mengstr/aytabtu/DiyLC/ROMdecoder1.png

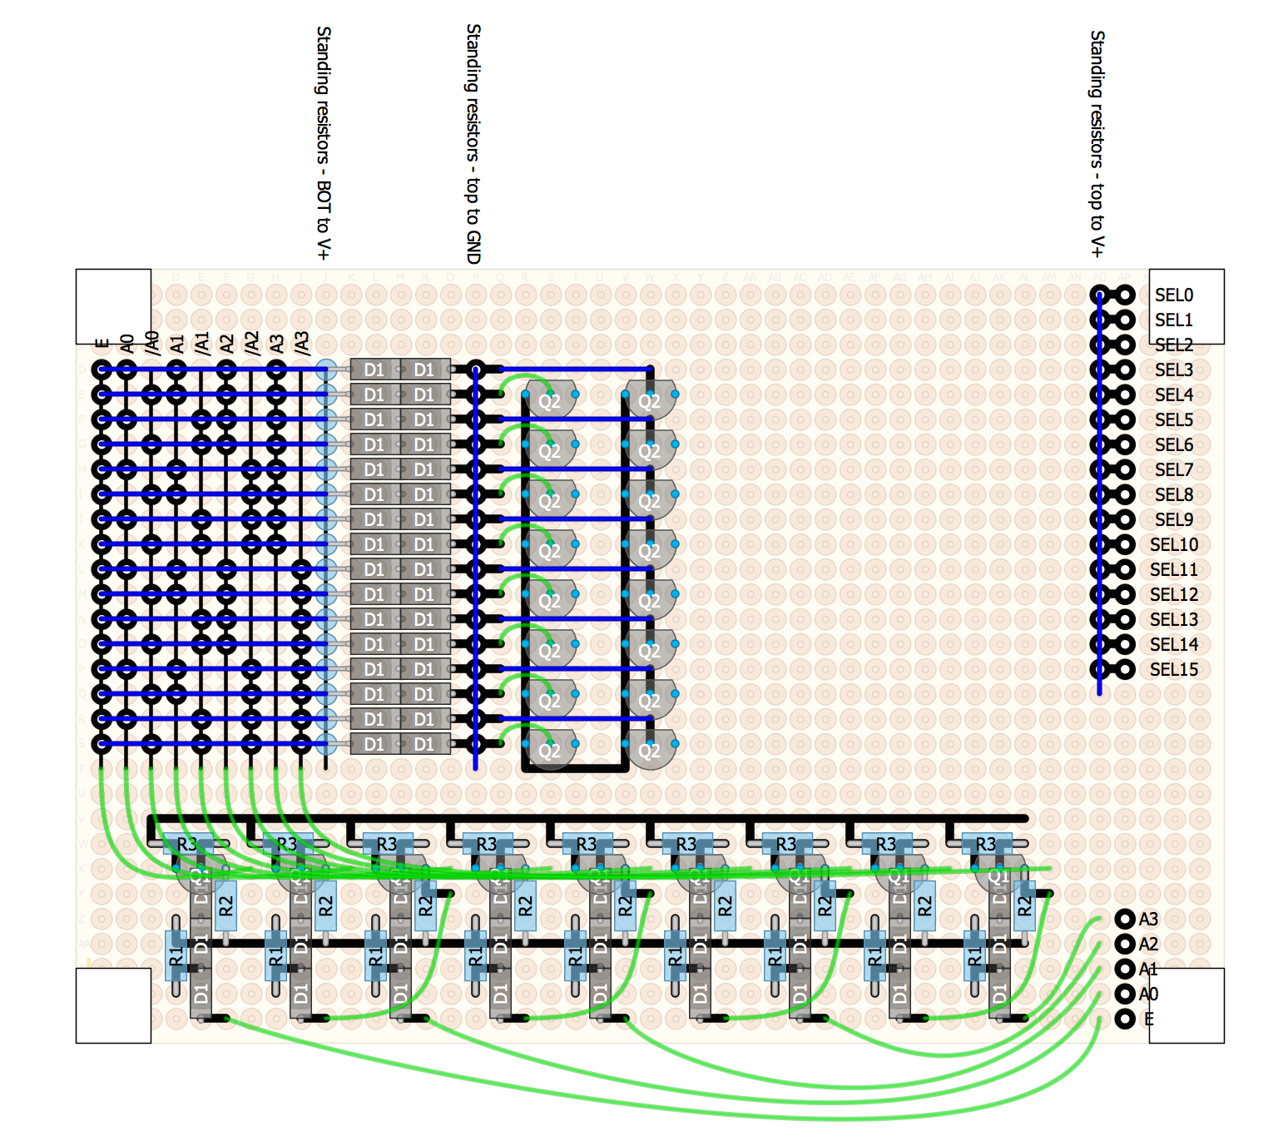
DiyLC/ROMdecoder1.png
