mengstr/aytabtu/DiyLC/UART-RX-D-LATCH.png

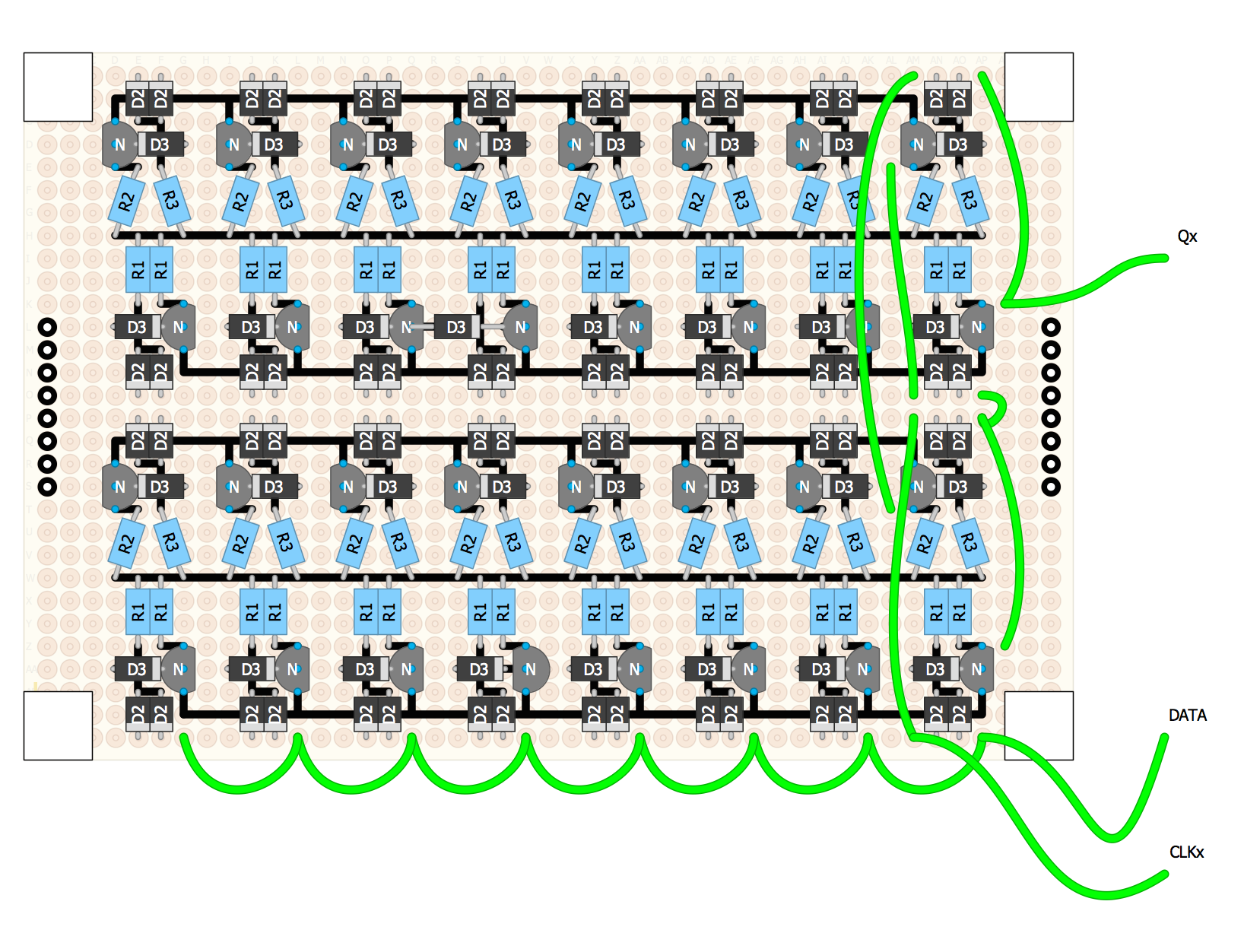
DiyLC/UART-RX-D-LATCH.png
