mengstr/aytabtu/DiyLC/UART-TX-RingCounter.png

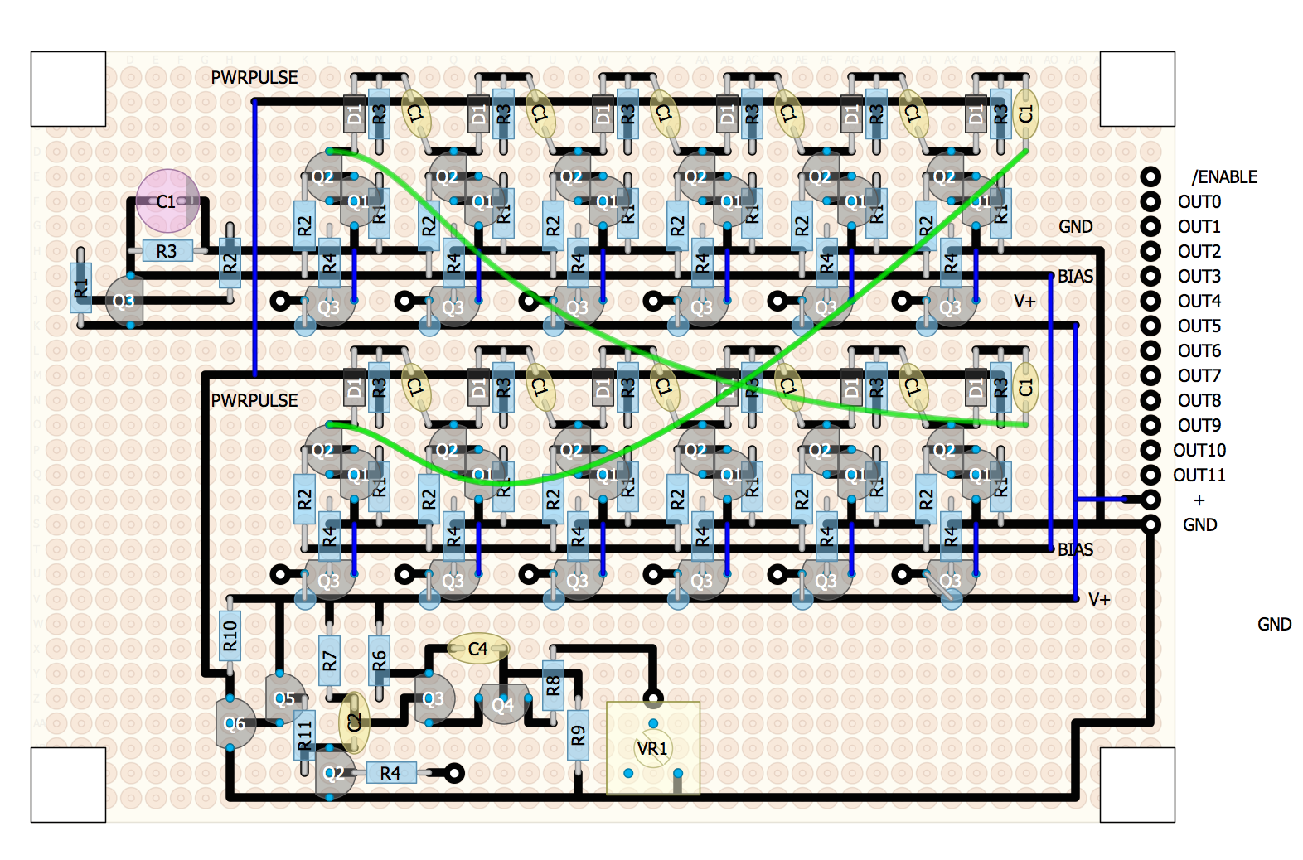
DiyLC/UART-TX-RingCounter.png
