mengstr/aytabtu/Images/4-to-16decoder-detail.jpg

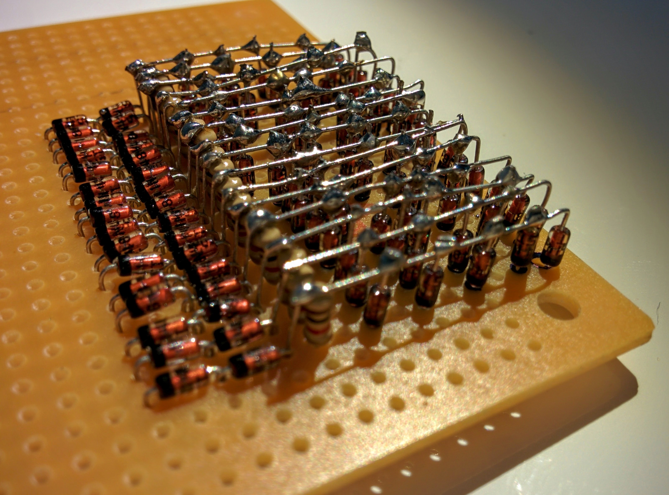
Images/4-to-16decoder-detail.jpg
