mengstr/aytabtu/Images/BusMonitorLeds.jpg

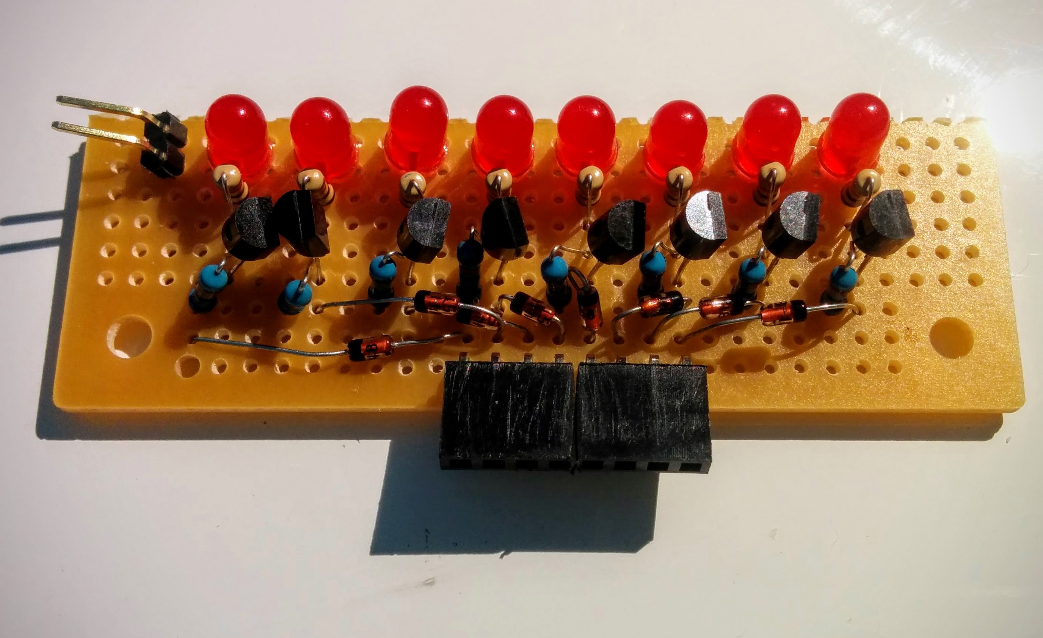
Images/BusMonitorLeds.jpg
