mengstr/aytabtu/Images/ClockGen4Phase1.png

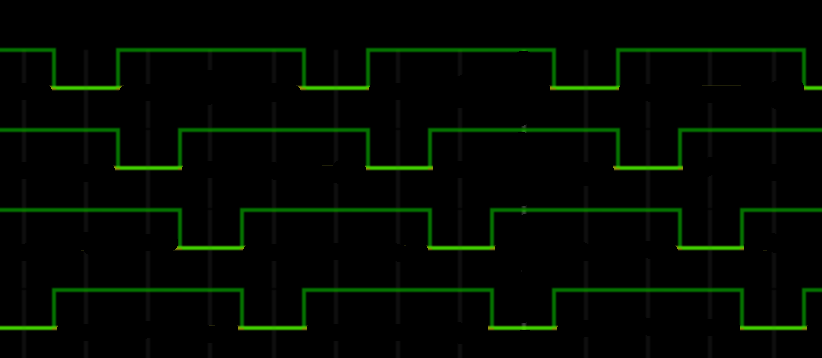
Images/ClockGen4Phase1.png
