mengstr/aytabtu/Images/ClockGenDiagram.png

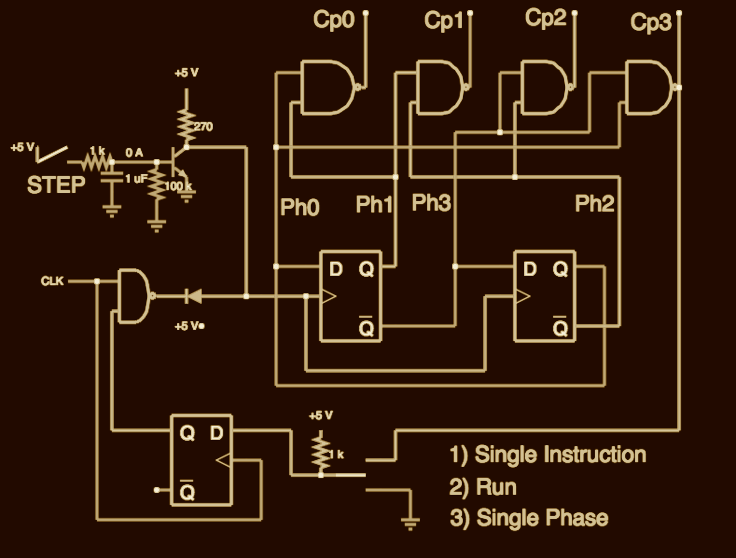
Images/ClockGenDiagram.png
