mengstr/aytabtu/Images/ClockGenPCB.jpg

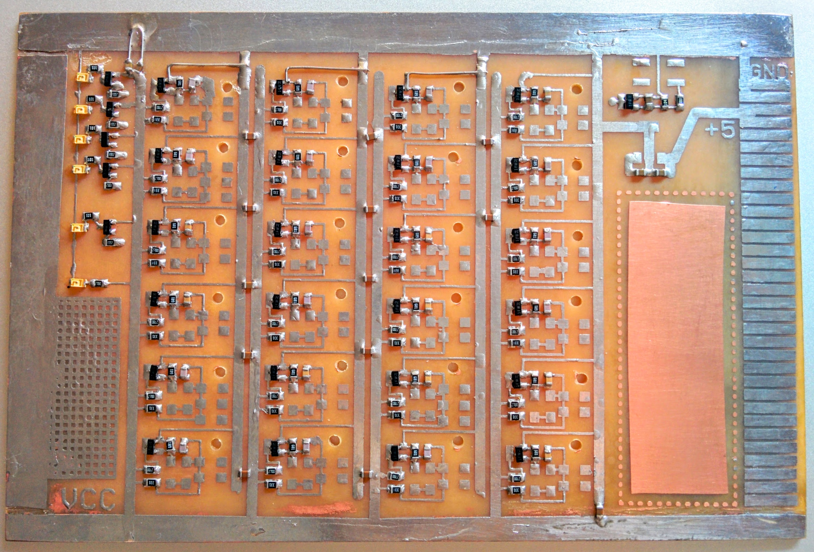
Images/ClockGenPCB.jpg
