mengstr/aytabtu/Images/ClockGenPCBdetail.jpg

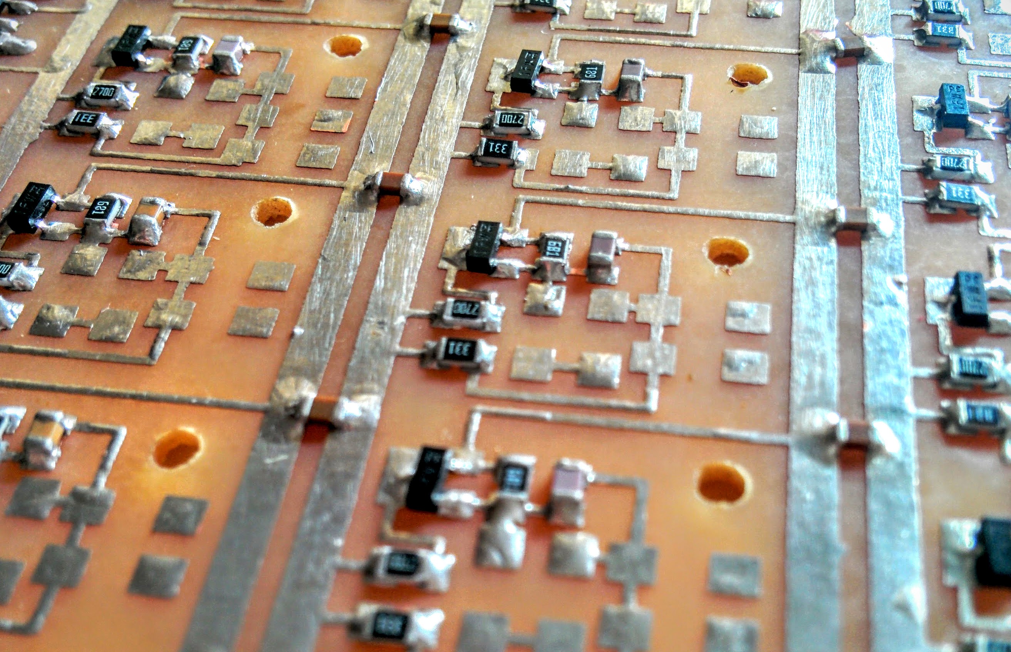
Images/ClockGenPCBdetail.jpg
