mengstr/aytabtu/Images/Divider-Scho.jpg

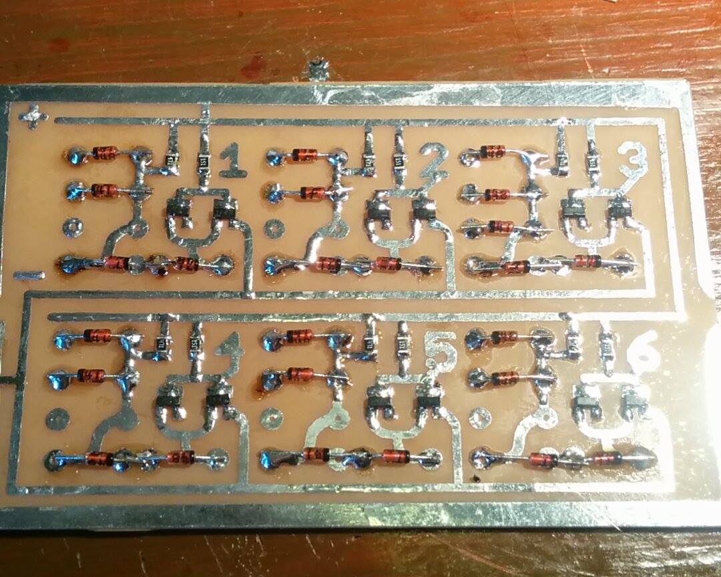
Images/Divider-Scho.jpg
