mengstr/aytabtu/Images/FastNandPCB.jpg

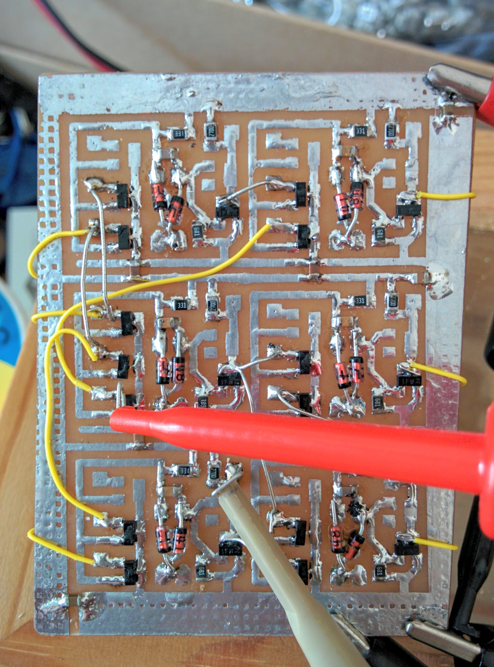
Images/FastNandPCB.jpg
