mengstr/aytabtu/Images/Hex4NANDs.jpg

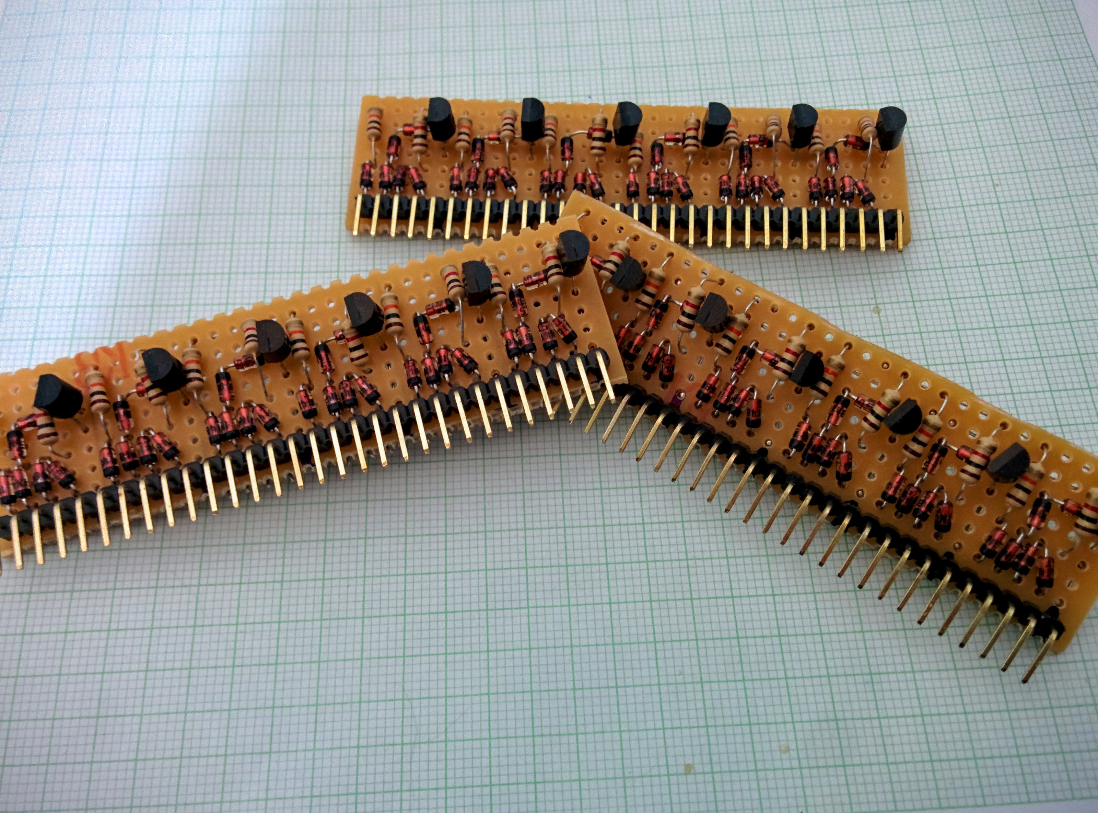
Images/Hex4NANDs.jpg
