mengstr/aytabtu/Images/NAND2_5v.png

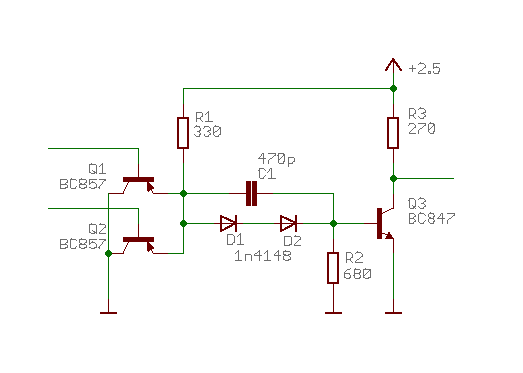
Images/NAND2_5v.png
