mengstr/aytabtu/Images/OctalTransparentDlatch-Bot.jpg

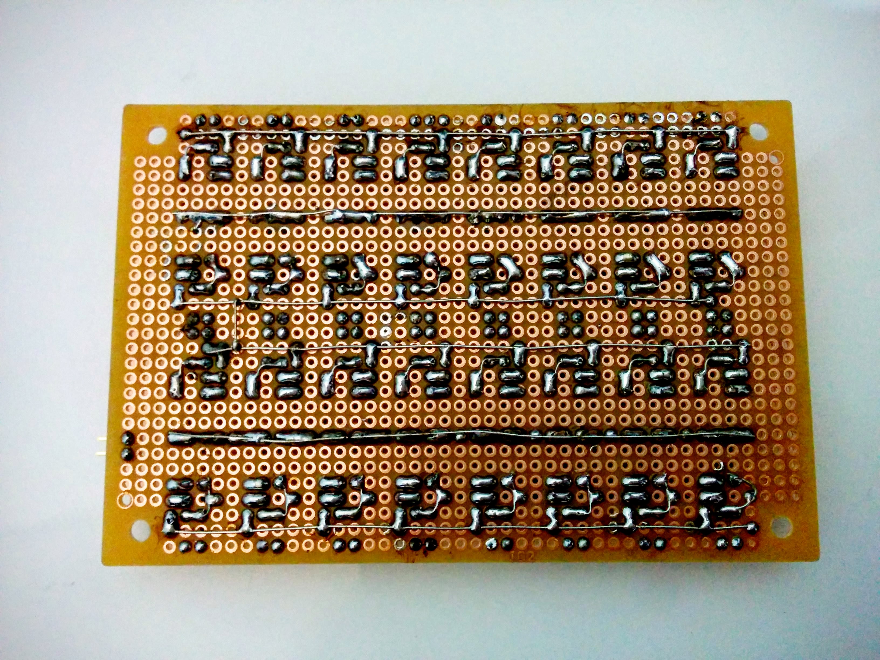
Images/OctalTransparentDlatch-Bot.jpg
