mengstr/aytabtu/Images/OctalTransparentDlatch-Top.jpg

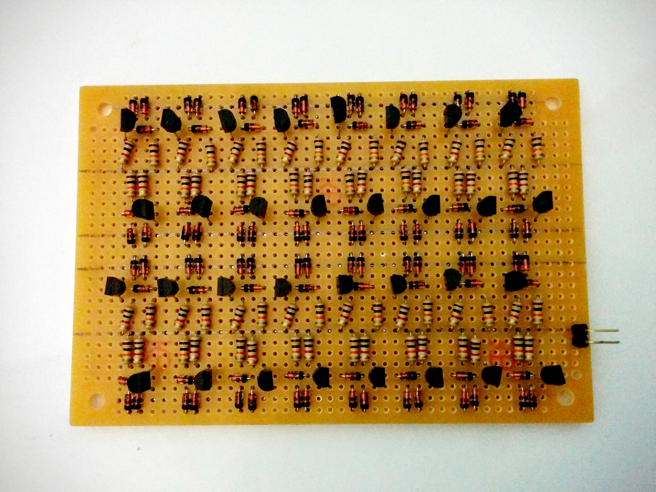
Images/OctalTransparentDlatch-Top.jpg
