mengstr/aytabtu/Images/UART-RX internal module routing.png

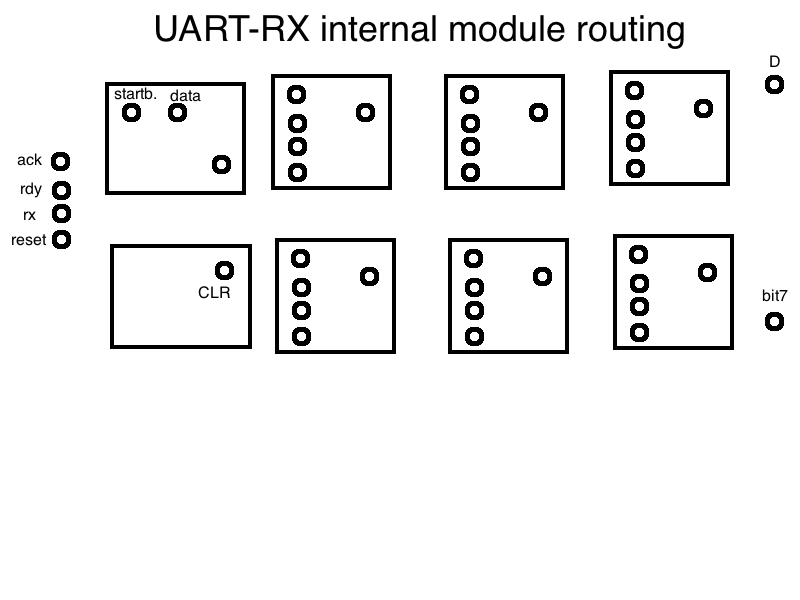
Images/UART-RX internal module routing.png
