mengstr/aytabtu/Images/UART-RX-D-LATCH.png

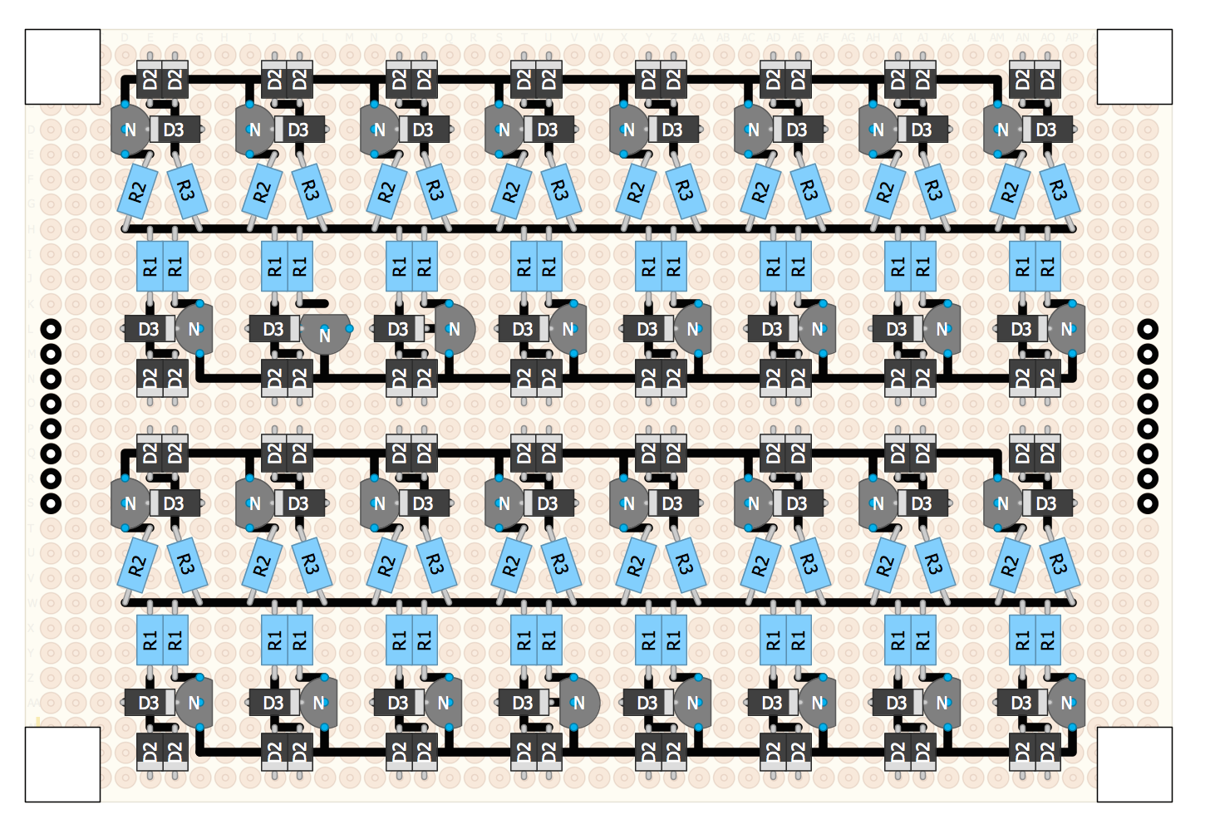
Images/UART-RX-D-LATCH.png
