mengstr/aytabtu/Images/UART-RX-timing1.jpg

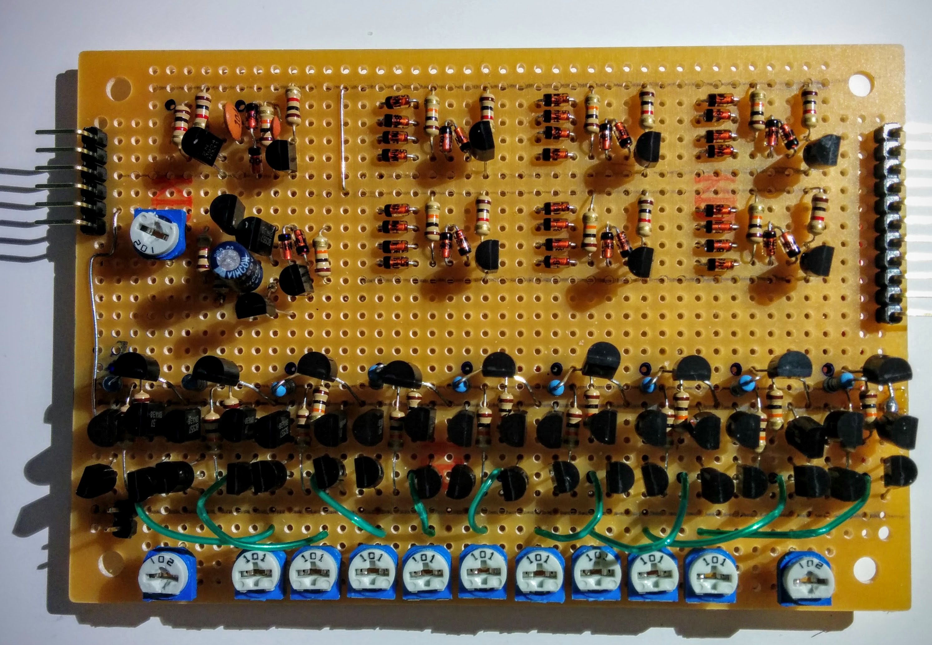
Images/UART-RX-timing1.jpg
