mengstr/aytabtu/Images/UART-RX-timing2.jpg

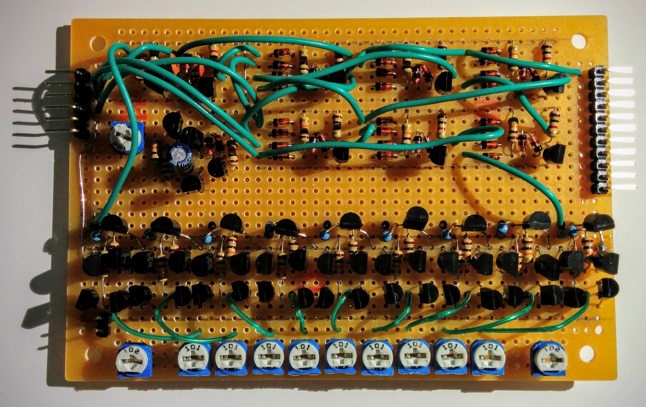
Images/UART-RX-timing2.jpg
