mengstr/aytabtu/Images/UART-TX-RingCounter.png

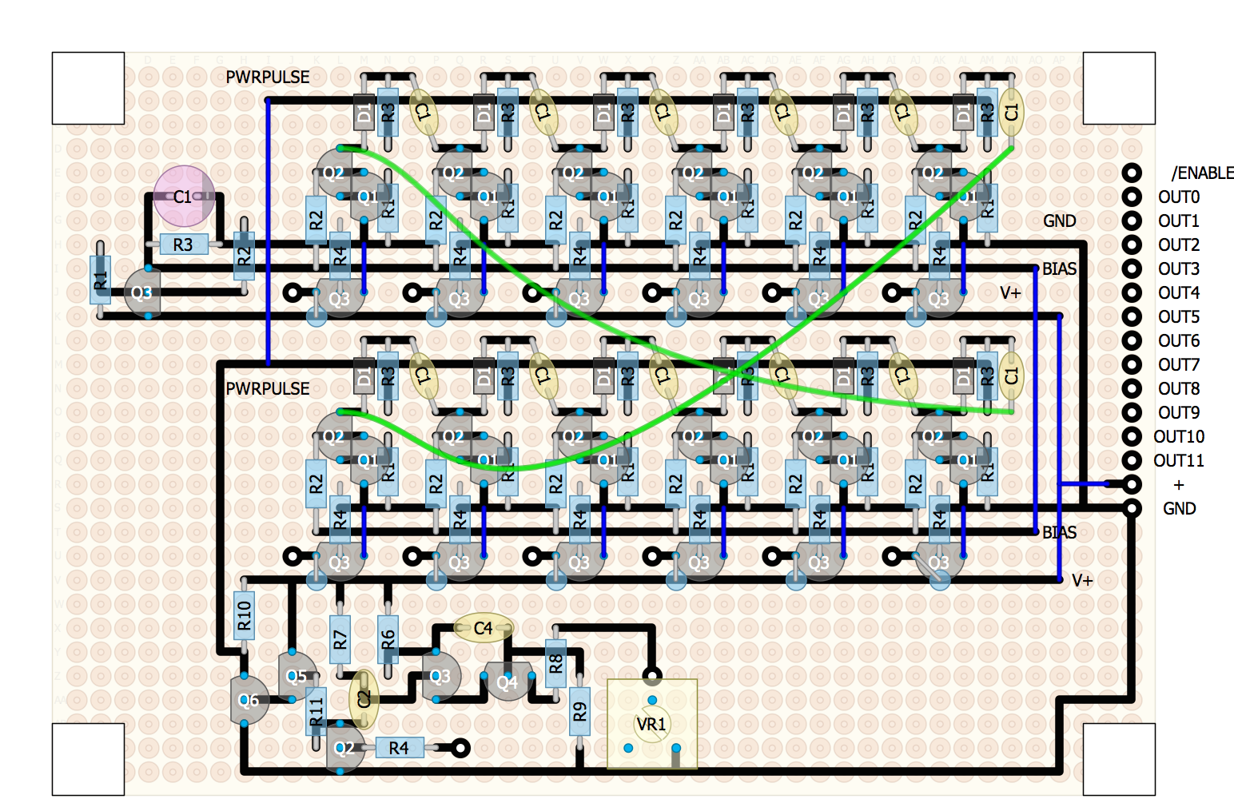
Images/UART-TX-RingCounter.png
