mengstr/aytabtu/Doc/InstructionSet.png

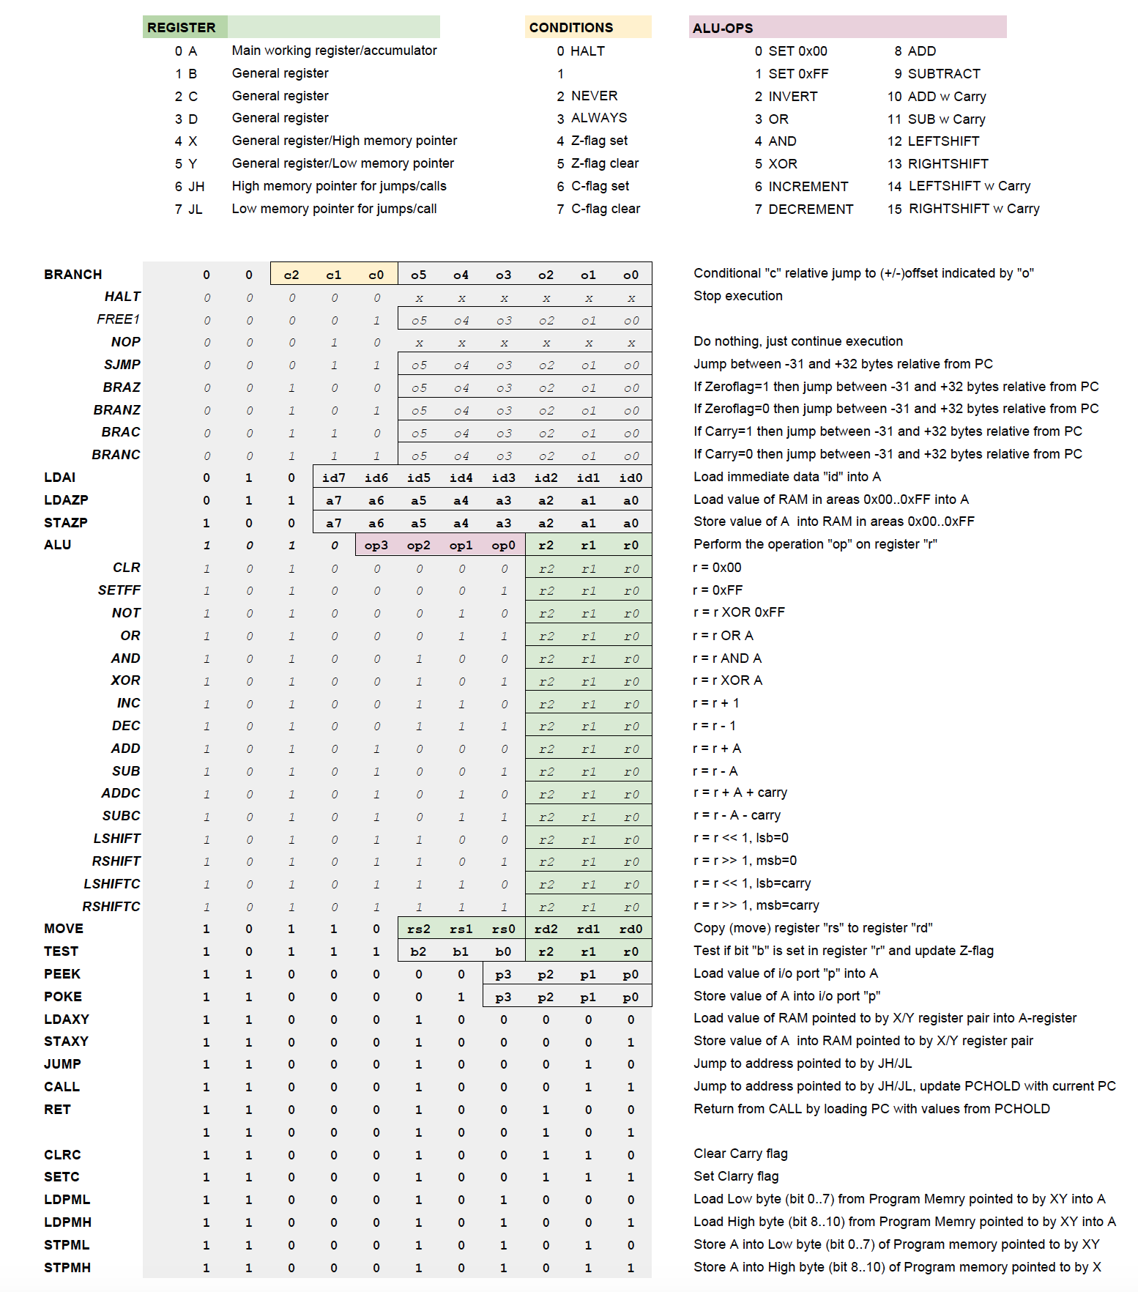
Doc/InstructionSet.png
