mengstr/aytabtu/Images/ALUSliceTest.jpg

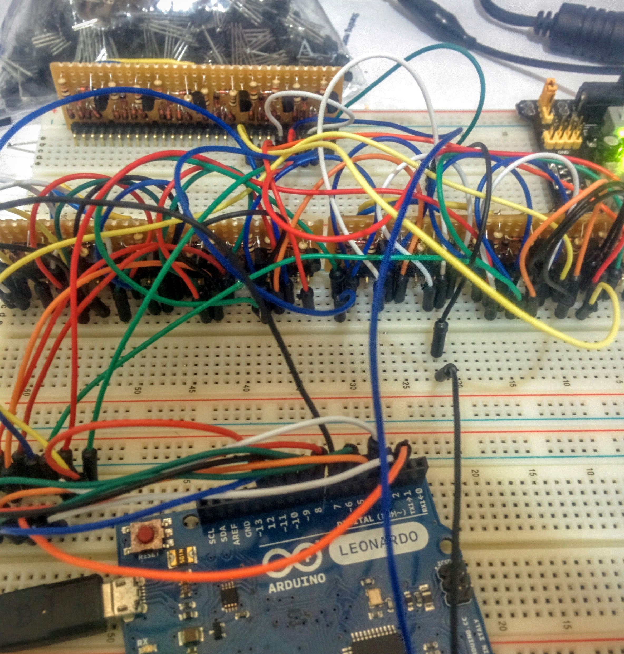
Images/ALUSliceTest.jpg
