mengstr/aytabtu/Images/TestingComparatorForUARTrx.jpg

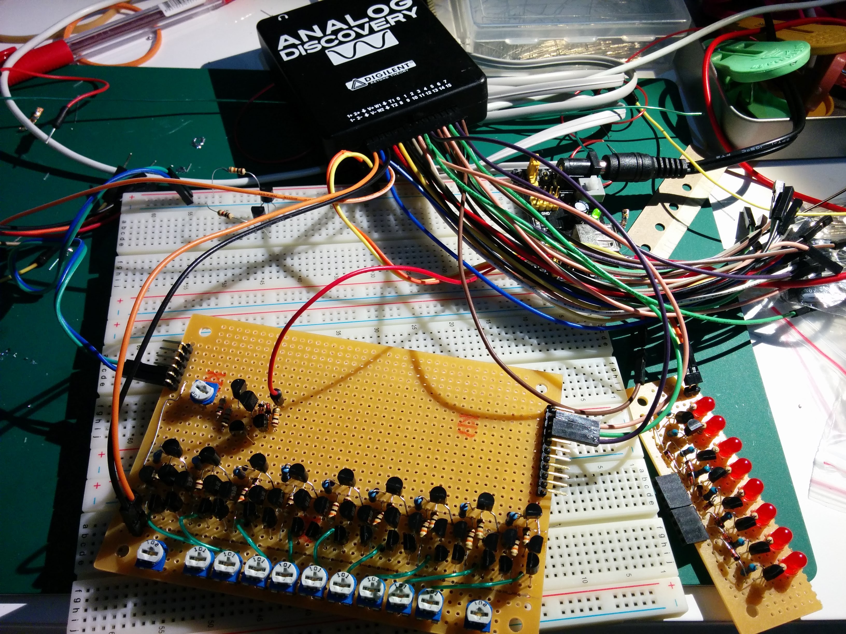
Images/TestingComparatorForUARTrx.jpg
