mengstr/aytabtu/Spice/Strip/Pmem-driver-test.asc

C1: cap; 1n
C2: cap; 100p
C3: cap; 100p
C4: cap; 100p
C5: cap; 100p
C6: cap; 100p
C7: cap; 100p
C8: cap; 100p
C9: cap; 100p
C10: cap; 100p
C11: cap; 100p
C12: cap; 100p
C13: cap; 100p
C14: cap; 100p
C15: cap; 100p
C16: cap; 100p
C17: cap; 100p
C18: cap; 100p
D1: schottky; BAT54
D2: diode; 1N4148
D3: schottky; BAT54
D4: diode; 1N4148
D5: schottky; BAT54
D6: diode; 1N4148
D7: schottky; BAT54
D8: schottky; BAT54
D9: diode; 1N4148
D10: diode; 1N4148
D11: schottky; BAT54
D12: diode; 1N4148
D13: schottky; BAT54
D14: diode; 1N4148
D15: schottky; BAT54
D16: diode; 1N4148
D17: schottky; BAT54
D18: diode; 1N4148
D19: schottky; BAT54
D20: diode; 1N4148
D21: schottky; BAT54
D22: diode; 1N4148
D23: schottky; BAT54
D24: diode; 1N4148
D25: schottky; BAT54
D26: diode; 1N4148
D27: schottky; BAT54
D28: diode; 1N4148
D29: schottky; BAT54
D30: diode; 1N4148
D31: schottky; BAT54
D32: diode; 1N4148
Q1: npn; BC847B
Q2: npn; BC847B
Q3: pnp; BC857B
Q4: npn; BC847B
Q5: npn; BC847B
Q6: npn; BC847B
Q7: npn; BC847B
Q8: npn; BC847B
Q9: npn; BC847B
Q10: npn; BC847B
Q11: npn; BC847B
Q12: npn; BC847B
Q13: npn; BC847B
Q14: npn; BC847B
Q15: npn; BC847B
Q16: npn; BC847B
Q17: npn; BC847B
Q18: npn; BC847B
R1: res; 150
R2: res; 470
R3: res; 470
R4: res; 150
R5: res; 470
R6: res; 150
R7: res; 150
R8: res; 470
R9: res; 470
R10: res; 150
R11: res; 470
R12: res; 150
R13: res; 470
R14: res; 150
R15: res; 470
R16: res; 150
R17: res; 470
R18: res; 150
R19: res; 470
R20: res; 150
R21: res; 470
R22: res; 150
R23: res; 470
R24: res; 150
R25: res; 470
R26: res; 150
R27: res; 470
R28: res; 150
R29: res; 470
R30: res; 150
R31: res; 470
R32: res; 150
R33: res; 470
V1: voltage; 3.3
V3: voltage; PULSE(3.3 0 0 1n 1n 300n 1u)
Named nets: 0, V+, WR, v+, in
.tran 3u
