mengstr/aytabtu/Spice/Strip/_FA1.asc

V1: voltage; PULSE(3.3 0 0 1n 1n 100n 200n)
V2: voltage; PULSE(3.2 0.1 0 1n 1n 200n 400n)
V3: voltage; PULSE(3.1 0.2 0 1n 1n 400n 800n)
V4: voltage; PULSE(3.1 0.2 0 1n 1n 2000n 4000n)
X1: FA1
Named nets: CO, SUM, 0, A, B, CI, /SUM
.tran 5888n
