mengstr/aytabtu/Spice/Tests/_PMemBoard.asc

D1: schottky; BAT54
D2: diode; 1N4148
D3: diode; 1N4148
D4: diode; 1N4148
D5: schottky; BAT54
D6: diode; 1N4148
D7: diode; 1N4148
D8: diode; 1N4148
D9: schottky; BAT54
D10: diode; 1N4148
D11: diode; 1N4148
D12: diode; 1N4148
Q1: npn; BC847B
Q2: npn; BC847B
Q3: npn; BC847B
R1: res; 150
R2: res; 150
R3: res; 150
R4: res; 150
R5: res; 150
R6: res; 150
R7: res; 150
R8: res; 150
R9: res; 150
R10: res; 150
R11: res; 150
R12: res; 470
R13: res; 150
R14: res; 470
R15: res; 150
R16: res; 470
R17: res; 150
V1: voltage; 3.3
V2: voltage; PULSE(3.3 0 0 1n 1n 20u 1 1)
V3: voltage; PULSE(3.3 0 0 1n 1n 300n 2u)
V4: voltage; PULSE(0 3.3 25u 1n 1n 5u 1 1)
X1: PMemBoard
Named nets: 0, V+, RESET, v+, RD, WR, BASE, OUT
.tran 1n 40u
