mengstr/aytabtu/Spice/Strip/_ProgMem.asc

R1: res; 150
R2: res; 150
R3: res; 150
R4: res; 150
R5: res; 150
R6: res; 150
R7: res; 150
R8: res; 150
R9: res; 150
R10: res; 150
R11: res; 150
V1: voltage; 3.3
V2: voltage; PULSE(0 3.3 1m 0 0 1u 1m 1)
V3: voltage; PULSE(0 3.3 0 0 0 330u 660u)
V4: voltage; 3.3
X1: ProgMem
Named nets: 0
.tran 10m
