mengstr/aytabtu/Spice/Tests/_QuadGen.asc

C1: cap; 1µ
C2: cap; 100n
C3: cap; 100n
C4: cap; 1n
C5: cap; 1n
C6: cap; 1n
C7: cap; 1n
D1: diode; 1N4148
D2: diode; 1N4148
D3: diode; 1N4148
D4: LED; NSCW100
D5: diode; 1N4148
D6: LED; NSCW100
D7: schottky; BAT54
D8: diode; 1N4148
D9: diode; 1N4148
D10: schottky; BAT54
D11: diode; 1N4148
D12: diode; 1N4148
D13: diode; 1N4148
D14: diode; 1N4148
D15: diode; 1N4148
D16: diode; 1N4148
D17: LED; NSCW100
D18: diode; 1N4148
D19: diode; 1N4148
D20: LED; NSCW100
D21: schottky; BAT54
D22: diode; 1N4148
D23: schottky; BAT54
D24: diode; 1N4148
D25: diode; 1N4148
D26: diode; 1N4148
D27: diode; 1N4148
D28: diode; 1N4148
D29: diode; 1N4148
D30: diode; 1N4148
D31: LED; NSCW100
D32: diode; 1N4148
D33: diode; 1N4148
D34: LED; NSCW100
D35: schottky; BAT54
D36: schottky; BAT54
D37: schottky; BAT54
D38: diode; 1N4148
D39: diode; 1N4148
D40: diode; 1N4148
D41: diode; 1N4148
D42: diode; 1N4148
D43: diode; 1N4148
D44: diode; 1N4148
D45: LED; NSCW100
D46: diode; 1N4148
D47: diode; 1N4148
D48: LED; NSCW100
D49: schottky; BAT54
D50: diode; 1N4148
D51: schottky; BAT54
D52: diode; 1N4148
D53: diode; 1N4148
D54: diode; 1N4148
D55: diode; 1N4148
D56: diode; 1N4148
D57: diode; 1N4148
D58: schottky; BAT54
D59: diode; 1N4148
D60: diode; 1N4148
D61: diode; 1N4148
D62: diode; 1N4148
D63: diode; 1N4148
D64: schottky; BAT54
D65: diode; 1N4148
D66: schottky; BAT54
D67: diode; 1N4148
D68: diode; 1N4148
D69: diode; 1N4148
D70: diode; 1N4148
D71: diode; 1N4148
D72: schottky; BAT54
D73: schottky; BAT54
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
V1: voltage; PULSE(0 3 0 5n 5n 100n 200n)
V2: voltage; 3
X1: QuadGen
X2: QuadGen-Sil
X3: QuadGen-MT15
Named nets: clk0, clk90, clk180, clk270, 0, v+, CLK, clk0sil, clk90sil, clk180sil, clk270sil, LED+SCH, 2D+SCH470, LED+Si, 2D+SCH680, clk270-MT, clk180-MT, clk90-MT, clk0-MT
.tran 1us
