mengstr/aytabtu/Spice/Strip/ALU1.asc

V1: voltage; 3.3
X1: Nand5Clamp
X2: Nand5Clamp
X3: Nand5Clamp
X4: Nand5Clamp
X5: Nand5Clamp
X6: Nand5Clamp
X7: Nand5Clamp
X8: Nand5Clamp
X9: Nand5Clamp
X10: Nand5Clamp
X11: Nand5Clamp
X12: Nand5Clamp
X13: Nand5Clamp
Named nets: v+, A, B, SUM, CO, CI, 0
