mengstr/aytabtu/Spice/Strip/BakerClamps.asc

C1: cap; 100p
C2: cap; 100p
C3: cap; 100p
C4: cap; 100p
D1: diode; 1N4148
D2: diode; 1N4148
D3: schottky; BAT54
D4: diode; 1N4148
D5: diode; 1N4148
D6: diode; 1N4148
Q1: npn; 2N3904
Q2: npn; 2N3904
Q3: npn; 2N3904
Q4: npn; 2N3904
R1: res; 1k
R2: res; 220
R3: res; 220
R4: res; 220
R5: res; 220
R6: res; 1k
R7: res; 1k
R8: res; 1k
V1: voltage; 5
V2: voltage; PULSE(0 5 0 1n 1n 25ns 50ns)
Named nets: 0, v+, IN, C, D, A, b
.tran 1ns  1000ns
