mengstr/aytabtu/Spice/Tests/D-FlipFlop-Edge-MT15.asc

C1: cap; 220p
C2: cap; 220p
C4: cap; 220p
C5: cap; 220p
C6: cap; 220p
C7: cap; 220p
D21: diode; 1N4148
D22: diode; 1N4148
D23: diode; 1N4148
D25: diode; 1N4148
D29: diode; 1N4148
D31: diode; 1N4148
D33: diode; 1N4148
D34: diode; 1N4148
D35: diode; 1N4148
D37: diode; 1N4148
D38: diode; 1N4148
D39: diode; 1N4148
Q7: pnp; BC857B
Q8: pnp; BC857B
Q9: npn; BC847B
Q10: pnp; BC857B
Q11: pnp; BC857B
Q12: npn; BC847B
Q13: pnp; BC857B
Q16: pnp; BC857B
Q17: pnp; BC857B
Q18: npn; BC847B
Q19: pnp; BC857B
Q20: pnp; BC857B
Q21: npn; BC847B
Q22: pnp; BC857B
Q23: pnp; BC857B
Q24: npn; BC847B
Q25: pnp; BC857B
Q26: pnp; BC857B
Q27: npn; BC847B
R13: res; 820
R14: res; 330
R15: res; 390
R16: res; 820
R17: res; 330
R18: res; 390
R22: res; 820
R23: res; 330
R24: res; 390
R25: res; 820
R26: res; 330
R27: res; 390
R28: res; 820
R29: res; 330
R30: res; 390
R31: res; 820
R32: res; 330
R33: res; 390
Named nets: CLK, D, Q, /Q, V+, 0, v+
