mengstr/aytabtu/Spice/Tests/D-FlipFlop-Edge-Sil.asc

D1: diode; 1N4148
D2: diode; 1N4148
D3: LED; NSCW100
D4: LED; NSCW100
D5: LED; NSCW100
D6: diode; 1N4148
D7: diode; 1N4148
D8: diode; 1N4148
D9: LED; NSCW100
D10: LED; NSCW100
D11: LED; NSCW100
D12: diode; 1N4148
D13: diode; 1N4148
D14: diode; 1N4148
D15: diode; 1N4148
D16: diode; 1N4148
D17: diode; 1N4148
D18: diode; 1N4148
D19: diode; 1N4148
D20: diode; 1N4148
D24: diode; 1N4148
D26: diode; 1N4148
D30: diode; 1N4148
D32: diode; 1N4148
D36: diode; 1N4148
Q1: npn; BC847B
Q2: npn; BC847B
Q3: npn; BC847B
Q4: npn; BC847B
Q5: npn; BC847B
Q6: npn; BC847B
R1: res; 150
R2: res; 470
R3: res; 150
R4: res; 470
R5: res; 150
R6: res; 470
R7: res; 150
R8: res; 470
R9: res; 150
R10: res; 470
R11: res; 150
R12: res; 470
Named nets: 0, v+, CLK, D, Q, /Q, V+
