mengstr/aytabtu/Spice/Tests/D-FlipFlop-Edge.asc

D1: schottky; BAT54
D2: diode; 1N4148
D3: diode; 1N4148
D4: diode; 1N4148
D6: diode; 1N4148
D7: schottky; BAT54
D8: diode; 1N4148
D9: diode; 1N4148
D10: diode; 1N4148
D12: diode; 1N4148
D13: schottky; BAT54
D14: diode; 1N4148
D15: diode; 1N4148
D16: diode; 1N4148
D17: diode; 1N4148
D18: diode; 1N4148
D19: schottky; BAT54
D20: diode; 1N4148
D21: diode; 1N4148
D22: diode; 1N4148
D24: diode; 1N4148
D25: schottky; BAT54
D26: diode; 1N4148
D27: diode; 1N4148
D28: diode; 1N4148
D30: diode; 1N4148
D31: schottky; BAT54
D32: diode; 1N4148
D33: diode; 1N4148
D34: diode; 1N4148
D36: diode; 1N4148
Q1: npn; BC847B
Q2: npn; BC847B
Q3: npn; BC847B
Q4: npn; BC847B
Q5: npn; BC847B
Q6: npn; BC847B
R1: res; 150
R2: res; 470
R3: res; 150
R4: res; 470
R5: res; 150
R6: res; 470
R7: res; 150
R8: res; 470
R9: res; 150
R10: res; 470
R11: res; 150
R12: res; 470
Named nets: 0, v+, CLK, D, Q, /Q, V+
