mengstr/aytabtu/Spice/Strip/Decoder4to16.asc

V1: voltage; 3.3
V2: voltage; PULSE(0 3.3 1u 5n 5n 1u 2u)
V3: voltage; PULSE(0 3.3 2u 5n 5n 2u 4u)
V4: voltage; PULSE(0 3.3 4u 5n 5n 4u 8u)
V5: voltage; PULSE(0 3.3 8u 5n 5n 8u 16u)
V6: voltage; PULSE(0 3.3 0.4u 5n 5n 0.1u 1u)
X1: Nand5Clamp
X2: Nand5Clamp
X3: Nand5Clamp
X4: Nand5Clamp
X5: Nand5Clamp
X6: Nand5Clamp
X7: Nand5Clamp
X8: Nand5Clamp
X9: Nand5Clamp
X10: Nand5Clamp
X11: Nand5Clamp
X12: Nand5Clamp
X13: Nand5Clamp
X14: Nand5Clamp
X15: Nand5Clamp
X16: Nand5Clamp
X17: Nand5Clamp
X18: Nand5Clamp
X19: Nand5Clamp
X20: Nand5Clamp
X21: Nand5Clamp
X22: Nand5Clamp
X23: Nand5Clamp
X24: Nand5Clamp
X25: Nand5Clamp
X26: Nand5Clamp
X27: Nand5Clamp
X28: Nand5Clamp
X29: Nand5Clamp
X30: Nand5Clamp
X31: Nand5Clamp
X32: Nand5Clamp
X33: Nand5Clamp
X34: Nand5Clamp
X35: Nand5Clamp
X36: Nand5Clamp
X37: Nand5Clamp
X38: Nand5Clamp
X39: Nand5Clamp
X40: Nand5Clamp
X41: Nand5Clamp
X42: Nand5Clamp
Named nets: 0, v+, ENABLE, Q0, Q1, Q2, Q3, Q4, Q5, Q6, Q7, Q8, Q9, Q10, Q11, Q12, Q13, Q14, Q15, EOUT
.tran 1n 18u
