mengstr/aytabtu/Spice/Tests/FanOutTest.asc

D1: diode; 1N4148
D2: diode; 1N4148
D3: schottky; BAT54
D4: LED; NSCW100
D5: diode; 1N4148
D6: diode; 1N4148
D7: schottky; BAT54
D8: diode; 1N4148
D9: diode; 1N4148
D10: diode; 1N4148
D11: diode; 1N4148
D12: diode; 1N4148
D13: diode; 1N4148
D14: schottky; BAT54
D15: diode; 1N4148
D16: diode; 1N4148
D17: diode; 1N4148
D18: schottky; BAT54
D19: diode; 1N4148
D20: diode; 1N4148
D21: diode; 1N4148
D22: schottky; BAT54
D23: diode; 1N4148
D24: diode; 1N4148
D25: diode; 1N4148
D26: schottky; BAT54
D27: diode; 1N4148
D28: diode; 1N4148
D29: diode; 1N4148
D30: schottky; BAT54
D31: diode; 1N4148
D32: diode; 1N4148
D33: diode; 1N4148
D34: schottky; BAT54
D35: diode; 1N4148
D36: schottky; BAT54
D37: diode; 1N4148
D38: diode; 1N4148
D39: schottky; BAT54
D40: diode; 1N4148
D41: diode; 1N4148
D42: diode; 1N4148
D43: schottky; BAT54
D44: diode; 1N4148
D45: diode; 1N4148
D46: diode; 1N4148
D47: schottky; BAT54
D48: diode; 1N4148
D49: diode; 1N4148
D50: diode; 1N4148
D51: schottky; BAT54
D52: diode; 1N4148
D53: diode; 1N4148
D54: diode; 1N4148
D55: schottky; BAT54
D56: diode; 1N4148
D57: diode; 1N4148
D58: diode; 1N4148
D59: diode; 1N4148
D60: diode; 1N4148
D61: diode; 1N4148
D62: diode; 1N4148
D63: schottky; BAT54
D64: diode; 1N4148
D65: diode; 1N4148
D66: diode; 1N4148
D67: schottky; BAT54
D68: diode; 1N4148
D69: diode; 1N4148
D70: diode; 1N4148
D71: schottky; BAT54
D72: diode; 1N4148
D73: diode; 1N4148
D74: diode; 1N4148
D75: schottky; BAT54
D76: diode; 1N4148
D77: diode; 1N4148
D78: diode; 1N4148
D80: schottky; BAT54
D81: schottky; BAT54
D82: diode; 1N4148
D84: schottky; BAT54
D85: LED; NSCW100
D86: schottky; BAT54
D87: diode; 1N4148
D88: diode; 1N4148
D89: diode; 1N4148
D139: schottky; BAT54
D140: diode; 1N4148
D143: diode; 1N4148
D145: diode; 1N4148
Q1: npn; BC847B
Q2: npn; BC847B
Q3: npn; BC847B
Q4: npn; BC847B
Q5: npn; BC847B
Q6: npn; BC847B
Q7: npn; BC847B
Q8: npn; BC847B
Q9: npn; BC847B
Q10: npn; BC847B
Q11: npn; BC847B
Q12: npn; BC847B
Q13: npn; BC847B
Q14: npn; BC847B
Q15: npn; BC847B
Q16: npn; BC847B
Q17: npn; BC847B
Q18: npn; BC847B
Q19: npn; BC847B
Q20: npn; BC847B
Q21: npn; BC847B
Q22: npn; BC847B
Q23: npn; BC847B
Q24: npn; BC847B
Q25: npn; BC847B
Q26: npn; BC847B
Q27: npn; BC847B
R1: res; 150
R2: res; 470
R3: res; 150
R4: res; 150
R5: res; 470
R6: res; 470
R7: res; 150
R8: res; 470
R9: res; 150
R10: res; 470
R11: res; 150
R12: res; 470
R13: res; 150
R14: res; 150
R15: res; 470
R16: res; 470
R17: res; 150
R18: res; 470
R19: res; 150
R20: res; 470
R21: res; 150
R22: res; 470
R23: res; 150
R24: res; 470
R25: res; 150
R26: res; 470
R27: res; 150
R28: res; 470
R29: res; 150
R30: res; 470
R31: res; 150
R32: res; 470
R33: res; 150
R34: res; 470
R35: res; 150
R36: res; 470
R37: res; 150
R38: res; 470
R39: res; 58
R40: res; 760
R41: res; 470
R42: res; 150
R43: res; 680
R44: res; 4k
R45: res; 0.01
R48: res; 470
R58: res; 150
R59: res; 470
R90: res; 0.01
R91: res; 0.01
R92: res; 0.01
R93: res; 0.01
R105: res; 0.01
V1: voltage; PULSE(0 3.3 10ns 10n 10n 250n 500n)
V2: voltage; 3.3
Named nets: 0, v+, CLK, tt
.tran 1us
