mengstr/aytabtu/Spice/Strip/INV.asc

D1: schottky; BAT54
D2: diode; 1N4148
D3: diode; 1N4148
Q1: npn; BC847B
R1: res; 150
R2: res; 470
Named nets: 0, /Q, V+, I
