mengstr/aytabtu/Spice/Strip/INV1.asc

D1: schottky; BAT54
D2: diode; 1N4148
D3: diode; 1N4148
D4: diode; 1N4148
Q1: npn; BC847B
R1: res; 150
R2: res; 470
V1: voltage; 3.3
Named nets: 0, /Q, I
