mengstr/aytabtu/Spice/Tests/Nand5Clamp.asc

D1: diode; 1N4148
D2: diode; 1N4148
D3: schottky; BAT54
D4: diode; 1N4148
D5: diode; 1N4148
D6: diode; 1N4148
D7: diode; 1N4148
D8: diode; 1N4148
Q3: npn; BC847B
R4: res; 150
R7: res; 470
V1: voltage; 3.3
Named nets: 0, Q, A, B, C, D, E
