mengstr/aytabtu/Spice/Tests/NandBakerClamp.asc

D1: diode; 1N4148
D2: diode; 1N4148
D3: schottky; BAT54
D4: schottky; BAT54
D5: diode; 1N4148
D6: diode; 1N4148
D7: diode; 1N4148
D8: diode; 1N4148
D9: schottky; BAT54
D10: diode; 1N4148
D11: schottky; BAT54
D12: diode; 1N4148
D13: diode; 1N4148
D14: diode; 1N4148
D15: diode; 1N4148
D16: diode; 1N4148
Q1: npn; BC847B
Q2: npn; BC847B
Q3: npn; BC847B
Q4: npn; BC847B
R1: res; 150
R2: res; 470
R3: res; 150
R4: res; 150
R5: res; 470
R6: res; 150
R7: res; 470
R8: res; 470
V1: voltage; 3.3
V3: voltage; PULSE(1.2 3 0 1n 1n 25ns 50ns)
Named nets: 0, v+, C, d, e, f
.tran 1ns  200ns 95ns
