mengstr/aytabtu/Spice/Tests/PMemBoard.asc

D1: schottky; BAT54
D3: diode; 1N4148
D4: diode; 1N4148
D5: diode; 1N4148
Q1: npn; BC847B
R1: res; 470
R2: res; 150
WORD0: PMemWord
WORD1: PMemWord
WORD2: PMemWord
WORD3: PMemWord
WORD4: PMemWord
WORD5: PMemWord
WORD6: PMemWord
WORD7: PMemWord
WORD8: PMemWord
WORD9: PMemWord
WORD10: PMemWord
WORD11: PMemWord
WORD12: PMemWord
WORD13: PMemWord
WORD14: PMemWord
WORD15: PMemWord
Named nets: V+, RESET, WR, DI0, DI1, DI2, DI3, DI4, DI5, DI6, DI7, DI8, DI9, DI10, DO0, DO1, DO2, DO3, DO4, DO5, DO6, DO7, DO8, DO9, DO10, RD, Di3, Di4, SEL0, SEL1, SEL2, SEL4, SEL8, SEL12, SEL13, SEL9, SEL5, SEL6, SEL10, SEL14, SEL15, SEL11, SEL7, SEL3, IRD, 0
