mengstr/aytabtu/Spice/Tests/PMemCell.asc

D1: diode; 1N4148
D2: diode; 1N4148
D3: schottky; BAT54
D4: diode; 1N4148
D5: diode; 1N4148
D6: diode; 1N4148
D7: diode; 1N4148
D8: diode; 1N4148
D9: diode; 1N4148
D10: diode; 1N4148
D11: diode; 1N4148
Q1: npn; BC847B
Q2: npn; BC847B
Q3: npn; BC847B
R1: res; 22k
R2: res; 22k
R3: res; 4.7k
R4: res; 22k
R7: res; 470
Named nets: 0, DO, RD, DI, RESET, V+, WR, SEL, BASE
The output is OpenCollector giving that junction J1 should be LOW when inactive.  Since R7 is pulling up this junction 
both D5 and D4 must be high for DO to be activated.
Active high
[J1]
Active low
Active high
PROGRAM MEMORY
Slow Write Fast Read
As long as WR is low it is pulling the data down, thus inactivating 
it since D9 is only allowing a high sigal to pass.
(Not sure if D1 is really needed)
