mengstr/aytabtu/Spice/Tests/PMemWord.asc

CELL0: PMemCell
CELL1: PMemCell
CELL2: PMemCell
CELL3: PMemCell
CELL4: PMemCell
CELL5: PMemCell
CELL6: PMemCell
CELL7: PMemCell
CELL8: PMemCell
CELL9: PMemCell
CELL10: PMemCell
D1: schottky; BAT54
D2: diode; 1N4148
D3: diode; 1N4148
D4: diode; 1N4148
Q1: npn; BC847B
R1: res; 470
R2: res; 150
R3: res; 1
Named nets: V+, RESET, DI0, DO0, IRD, WR, SEL, RD, DI1, DO1, DI2, DO2, DI3, DO3, DI4, DO4, DI5, DO5, DI6, DO6, DI7, DO7, DI8, DO8, DI9, DO9, DI10, DO10, 0, rd, ABC
