mengstr/aytabtu/Spice/Tests/QuadGen-MT15.asc

X1: D-FlipFlop-Edge-MT15
X2: D-FlipFlop-Edge-MT15
Named nets: CLK, CLK90, CLK270, CLK0, CLK180, v+, V+
