mengstr/aytabtu/Spice/Tests/QuadGen-Sil.asc

X1: D-FlipFlop-Edge-Sil
X2: D-FlipFlop-Edge-Sil
Named nets: CLK, CLK90, CLK270, CLK0, CLK180, v+, V+
