mengstr/aytabtu/Spice/Tests/QuadGen.asc

X1: D-FlipFlop-Edge
X2: D-FlipFlop-Edge
Named nets: CLK, CLK90, CLK270, CLK0, CLK180, v+, V+
