mengstr/aytabtu/Spice/Tests/ROM.asc

D1: diode; 1N4148
D2: diode; 1N4148
D3: diode; 1N4148
D4: diode; 1N4148
D5: schottky; BAT54
Q1: npn; BC847B
R1: res; 470
R2: res; 1k
V1: voltage; 3.3
Named nets: CE, SEL, 0, RE
