mengstr/aytabtu/Spice/Tests/ROMBANK.asc

D1: diode; 1N4148
D2: diode; 1N4148
D3: diode; 1N4148
D4: diode; 1N4148
D5: diode; 1N4148
D6: diode; 1N4148
D7: diode; 1N4148
D8: diode; 1N4148
D9: diode; 1N4148
D10: diode; 1N4148
D11: diode; 1N4148
D12: diode; 1N4148
D13: schottky; BAT54
D14: diode; 1N4148
D15: diode; 1N4148
D16: schottky; BAT54
D17: diode; 1N4148
D18: diode; 1N4148
D19: schottky; BAT54
D20: diode; 1N4148
D21: diode; 1N4148
D22: schottky; BAT54
D23: diode; 1N4148
D24: diode; 1N4148
Q1: npn; BC847B
Q2: npn; BC847B
Q3: npn; BC847B
Q4: npn; BC847B
R1: res; 470
R2: res; 470
R3: res; 470
R4: res; 470
R5: res; 470
R6: res; 470
R7: res; 470
R8: res; 470
R9: res; 470
R10: res; 470
R11: res; 470
R12: res; 150
R13: res; 150
R14: res; 150
R15: res; 150
V1: voltage; 3.3
X1: ROM
X2: ROM
X3: ROM
X4: ROM
X5: ROM
X6: ROM
X7: ROM
X8: ROM
X9: ROM
X10: ROM
X11: ROM
X12: ROM
X13: ROM
X14: ROM
X15: ROM
X16: ROM
X17: Decoder4to16
Named nets: 0, out0, out1, out2, out3
.tran 1n 11us 8us
