mengstr/aytabtu/Spice/Tests/74HC/ALU1.asc

U1: 74hc00
U2: 74hc00
U3: 74hc00
U4: 74hc86
U5: 74hc86
U7: 74hc86
Named nets: A, Ci, Sum, Co, B, NOTB, A_NAND_B, A_XOR_B
.include 74HC.lib
