mengstr/aytabtu/BootstrappedChargingResistor.asc

C1: cap; 100n
D1: diode; 1N4148
Q1: pnp; 2N3906
Q2: npn; 2N3904
Q3: pnp; 2N3906
R1: res; 100k
R2: res; 1k
R3: res; 10k
R4: res; 56k
V1: voltage; 5
Named nets: 0, Out
.tran 0 250m 0 50u uic
