mengstr/aytabtu/clock-scaler.asc

C10: cap; 220p
C11: cap; 220p
C12: cap; 220p
C13: cap; 220p
C14: cap; 220p
C15: cap; 220p
C16: cap; 220p
C17: cap; 220p
C18: cap; 220p
C19: cap; 220p
C20: cap; 220p
C21: cap; 220p
C25: cap; 220p
C26: cap; 220p
C27: cap; 220p
C28: cap; 220p
C29: cap; 220p
C30: cap; 220p
C31: cap; 220p
C32: cap; 220p
C33: cap; 220p
D10: diode; 1N4148
D11: diode; 1N4148
D12: diode; 1N4148
D13: diode; 1N4148
D14: diode; 1N4148
D15: diode; 1N4148
D16: diode; 1N4148
D17: diode; 1N4148
D18: diode; 1N4148
D19: diode; 1N4148
D20: diode; 1N4148
D21: diode; 1N4148
D22: diode; 1N4148
D23: diode; 1N4148
D27: diode; 1N4148
D28: diode; 1N4148
D29: diode; 1N4148
D30: diode; 1N4148
D31: diode; 1N4148
D32: diode; 1N4148
D33: diode; 1N4148
D34: diode; 1N4148
D40: diode; 1N4148
D41: diode; 1N4148
D42: diode; 1N4148
D43: diode; 1N4148
D44: diode; 1N4148
D45: diode; 1N4148
D46: diode; 1N4148
D47: diode; 1N4148
D48: diode; 1N4148
D49: diode; 1N4148
D50: diode; 1N4148
D51: diode; 1N4148
D52: diode; 1N4148
D53: diode; 1N4148
D54: diode; 1N4148
D55: diode; 1N4148
D56: diode; 1N4148
D57: diode; 1N4148
D58: diode; 1N4148
D59: diode; 1N4148
D60: diode; 1N4148
D61: diode; 1N4148
D560: diode; 1N4148
D561: diode; 1N4148
Q3: npn; 2N3904
Q4: npn; 2N3904
Q10: npn; 2N3904
Q11: npn; 2N3904
Q12: npn; 2N3904
Q13: npn; 2N3904
Q14: npn; 2N3904
Q15: npn; 2N3904
Q20: npn; 2N3904
Q21: npn; 2N3904
Q22: pnp; 2N3906
Q23: npn; 2N3904
Q24: npn; 2N3904
Q25: npn; 2N3904
Q26: npn; 2N3904
Q27: npn; 2N3904
Q28: npn; 2N3904
Q29: npn; 2N3904
Q30: npn; 2N3904
Q48: pnp; 2N3906
R1: res; 500k
R27: res; 10K
R28: res; 10K
R29: res; 10K
R30: res; 10K
R37: res; 100K
R38: res; 10K
R39: res; 100K
R40: res; 10k
R41: res; 10k
R42: res; 100k
R43: res; 99k
R44: res; 10K
R45: res; 10K
R46: res; 100K
R47: res; 100K
R48: res; 100k
R49: res; 99k
R50: res; 10k
R51: res; 10k
R52: res; 10K
R53: res; 100K
R54: res; 100K
R55: res; 100k
R56: res; 99k
R57: res; 10k
R58: res; 10k
R66: res; 10K
R87: res; 10K
R88: res; 10K
R89: res; 10K
R90: res; 10K
R91: res; 100K
R92: res; 100K
R93: res; 100k
R94: res; 99k
R95: res; 10k
R96: res; 10k
R97: res; 10k
R98: res; 10k
R99: res; 100k
R100: res; 99k
R101: res; 100K
R102: res; 10K
R103: res; 100K
R104: res; 100K
R320: res; 100K
R371: res; 100k
R372: res; 10k
R373: res; 10k
R374: res; 99k
R375: res; 100k
R376: res; 10K
R377: res; 100K
R378: res; 100K
R379: res; 10k
R380: res; 10k
R381: res; 99k
R382: res; 10K
R383: res; 10K
V1: voltage; 12
V2: voltage; PULSE(0 12 .1 .000001 .000001 .00833333 .01666666)
Named nets: 0, 60HZ, NQC_0, QC_0, NQC_1, QC_1, +12V, NQC_2, QC_2, NQC_3, QC_3, NQD_0, QD_0, NQD_1, QD_1, NQD_2, QD_2
.tran 0.5 startup
A
B
C
D
E
